zanac86/lampolumo/lampo/Core/Src/OLED_Fonts.c

#include "OLED_Fonts.h"

font_t Font;

void OLED_FontSet(const uint8_t* new_font)
{
    Font.font     = new_font;
    Font.width    = (int16_t)fontbyte(0);
    Font.height   = (int16_t)fontbyte(1);
    Font.offset   = (int16_t)fontbyte(2);
    Font.numchars = (int16_t)fontbyte(3); // всего байт на один символ
    Font.inverted = NORMAL;
}

// MSX font 6x8
fontdatatype Font_MSX_6x8_rus1251[] =
{
    0x06, 0x08, 0x00, 0x07,
    0x06, 0x00, 0x00, 0x00, 0x00, 0x00, 0x00, //   0  00
    0x06, 0x00, 0x00, 0x00, 0x00, 0x00, 0x00, //   1  01
    0x06, 0x00, 0x00, 0x00, 0x00, 0x00, 0x00, //   2  02
    0x06, 0x00, 0x00, 0x00, 0x00, 0x00, 0x00, //   3  03
    0x06, 0x00, 0x00, 0x00, 0x00, 0x00, 0x00, //   4  04
    0x06, 0x00, 0x00, 0x00, 0x00, 0x00, 0x00, //   5  05
    0x06, 0x00, 0x00, 0x00, 0x00, 0x00, 0x00, //   6  06
    0x06, 0x00, 0x00, 0x00, 0x00, 0x00, 0x00, //   7  07
    0x06, 0x00, 0x00, 0x00, 0x00, 0x00, 0x00, //   8  08
    0x06, 0x00, 0x00, 0x00, 0x00, 0x00, 0x00, //   9  09
    0x06, 0x00, 0x00, 0x00, 0x00, 0x00, 0x00, //  10  0a
    0x06, 0x00, 0x00, 0x00, 0x00, 0x00, 0x00, //  11  0b
    0x06, 0x00, 0x00, 0x00, 0x00, 0x00, 0x00, //  12  0c
    0x06, 0x00, 0x00, 0x00, 0x00, 0x00, 0x00, //  13  0d
    0x06, 0x00, 0x00, 0x00, 0x00, 0x00, 0x00, //  14  0e
    0x06, 0x00, 0x00, 0x00, 0x00, 0x00, 0x00, //  15  0f
    0x06, 0x00, 0x00, 0x00, 0x00, 0x00, 0x00, //  16  10
    0x06, 0x00, 0x00, 0x00, 0x00, 0x00, 0x00, //  17  11
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
    0x06, 0x7c, 0x50, 0x20, 0x00, 0x7c, 0x00, // 251  fb
    0x06, 0x00, 0x7c, 0x50, 0x50, 0x20, 0x00, // 252  fc
    0x06, 0x28, 0x44, 0x54, 0x54, 0x38, 0x00, // 253  fd
    0x06, 0x7c, 0x10, 0x38, 0x44, 0x38, 0x00, // 254  fe
    0x06, 0x08, 0x54, 0x34, 0x14, 0x7c, 0x00, // 255  ff
};
