zanac86/lampolumo/lampo/Core/Inc/OLED_Icons.h

#ifndef ICONS_H_
#define ICONS_H_

#include <stdint.h>

#define NULL_ICON (void*)0

/* Icon in XBM */
extern const uint8_t icon_clock[];

extern const uint8_t arr_up[];
extern const uint8_t arr_dn[];

#endif /* ICONS_H_ */
