zanac86/lampolumo/lampo/Core/Src/OLED_Icons.c

#include "OLED_Icons.h"

/* Icon in XBM */
const uint8_t icon_clock[] = {24, 24, 0x00, 0x7F, 0x00, 0x00, 0x7F, 0x00, 0x00, 0x00, 0x18, 0x00, 0x7F,
                              0x38, 0xC0, 0xFF, 0x71, 0xE0, 0xC1, 0xFB, 0x70, 0x00, 0xDF, 0x18, 0x00,
                              0x0C, 0xDC, 0x00, 0x1C, 0xCC, 0x01, 0x18, 0x8E, 0x03, 0x38, 0x06, 0x07,
                              0x30, 0x06, 0x1E, 0x30, 0x06, 0x1C, 0x30, 0x06, 0x1C, 0x30, 0x06, 0x00,
                              0x30, 0x0E, 0x00, 0x38, 0x0C, 0x00, 0x18, 0x1C, 0x00, 0x1C, 0x18, 0x00,
                              0x0C, 0x70, 0x00, 0x07, 0xE0, 0xC1, 0x03, 0xC0, 0xFF, 0x01, 0x00, 0x7F,
                              0x00
                             };

const uint8_t arr_up[] =
{
    8,
    8,
    0x08,
    0x08,
    0x1C,
    0x1C,
    0x3E,
    0x3E,
    0x7F,
    0x7F,
};

const uint8_t arr_dn[] =
{
    8,
    8,
    0x7F,
    0x7F,
    0x3E,
    0x3E,
    0x1C,
    0x1C,
    0x08,
    0x08,
};
